Botond24/Code_Like_A_Bosch/video/20230930_123244.jpg

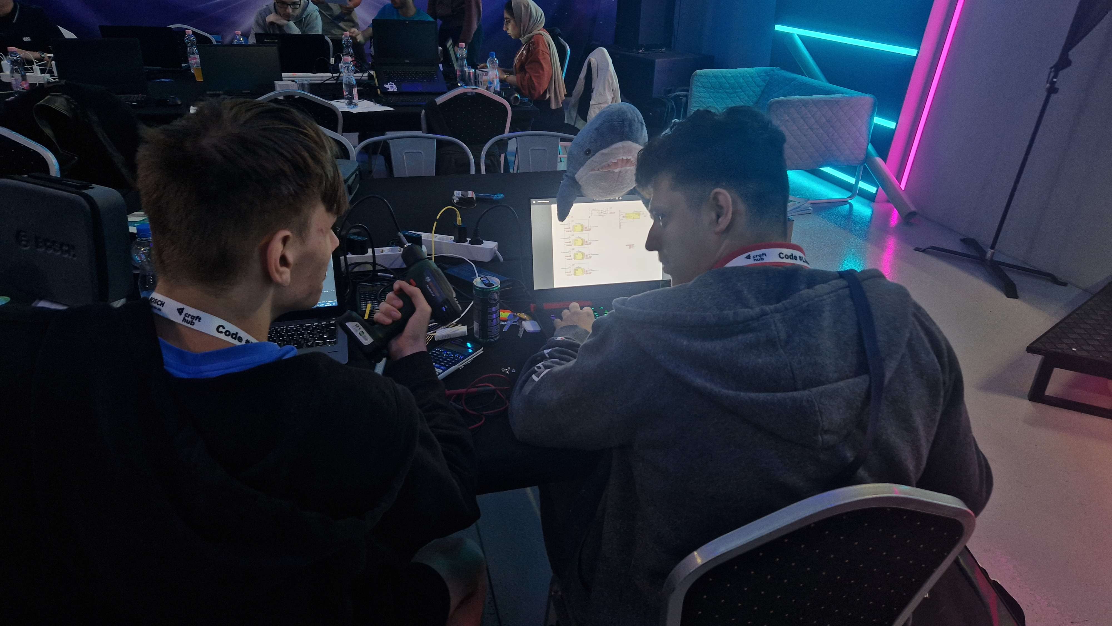
video/20230930_123244.jpg
